gou-th/ice40-vga-controller/digital/digital_image.png

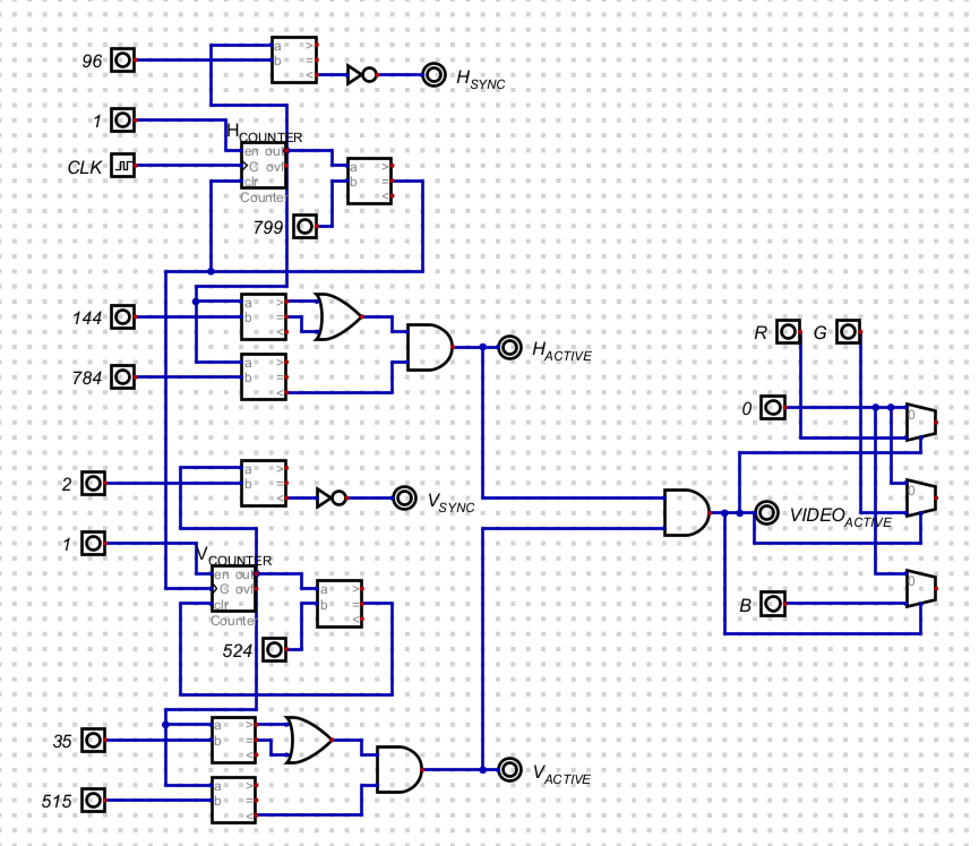
digital/digital_image.png
