gou-th/ice40-vga-controller/kicad/model/vga_3d_back.png

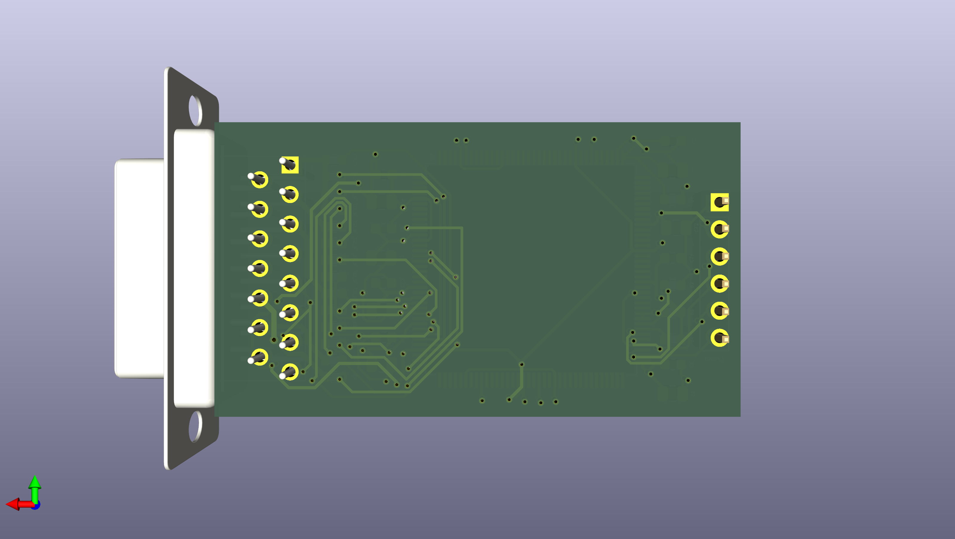
kicad/model/vga_3d_back.png
