gou-th/ice40-vga-controller/kicad/pcb/pcb_bottom_layer.png

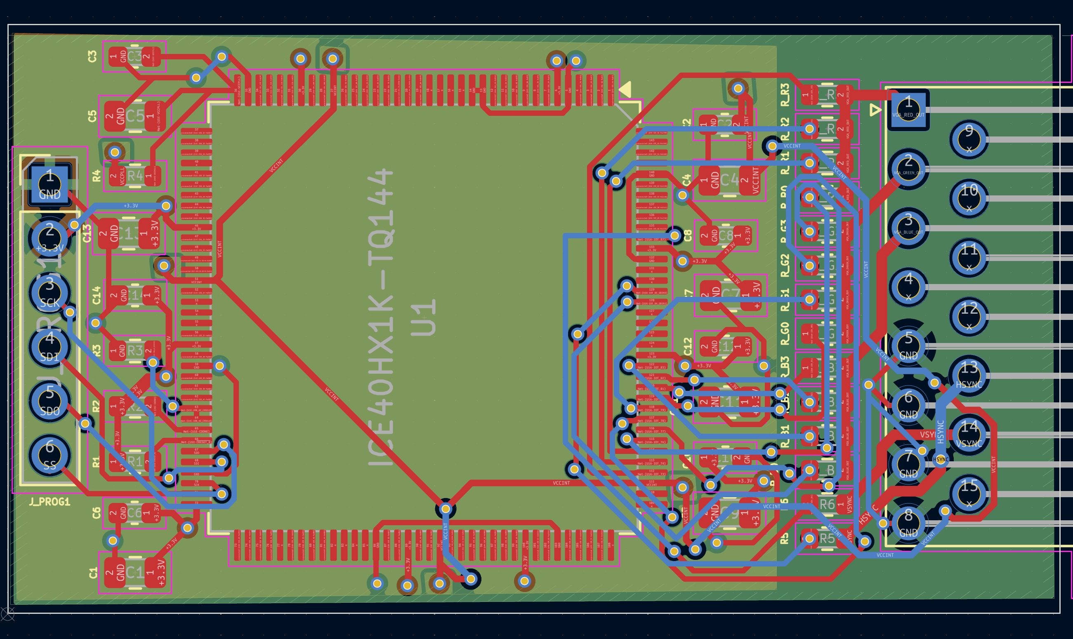
kicad/pcb/pcb_bottom_layer.png
