gou-th/ice40-vga-controller/systemverilog/sim/waveform/v_sync_end.png

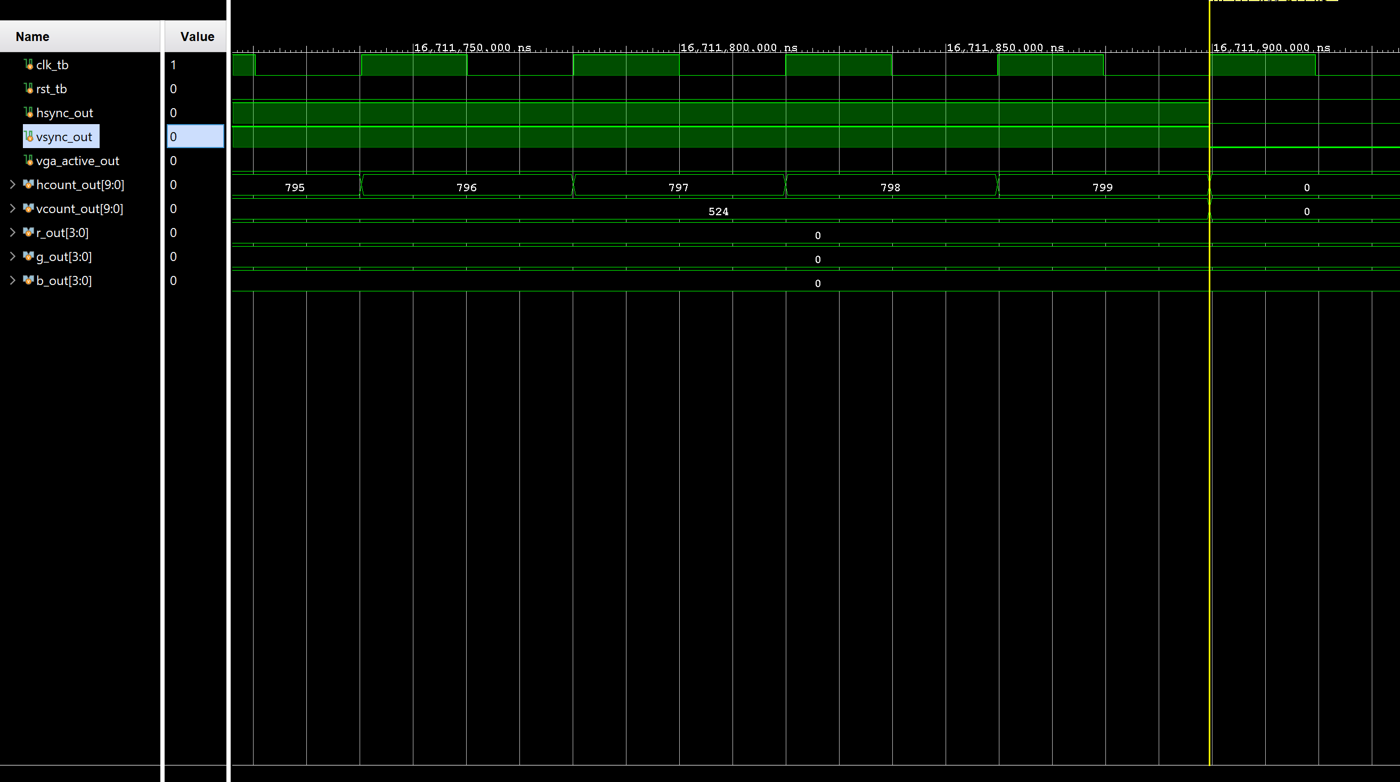
systemverilog/sim/waveform/v_sync_end.png
