gou-th/ice40-vga-controller/systemverilog/sim/waveform/v_sync_start.png

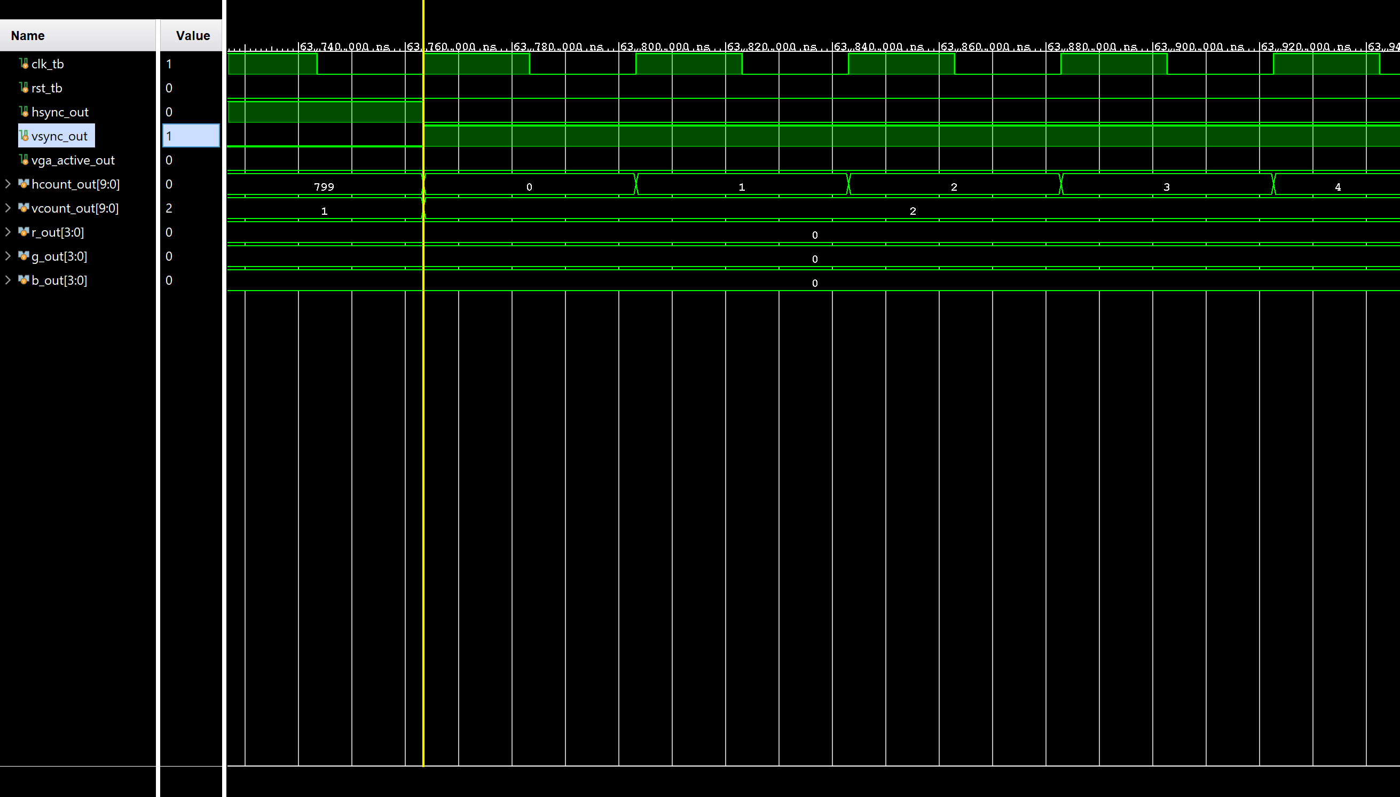
systemverilog/sim/waveform/v_sync_start.png
