gou-th/ice40-vga-controller/systemverilog/sim/waveform/vga_active_end.png

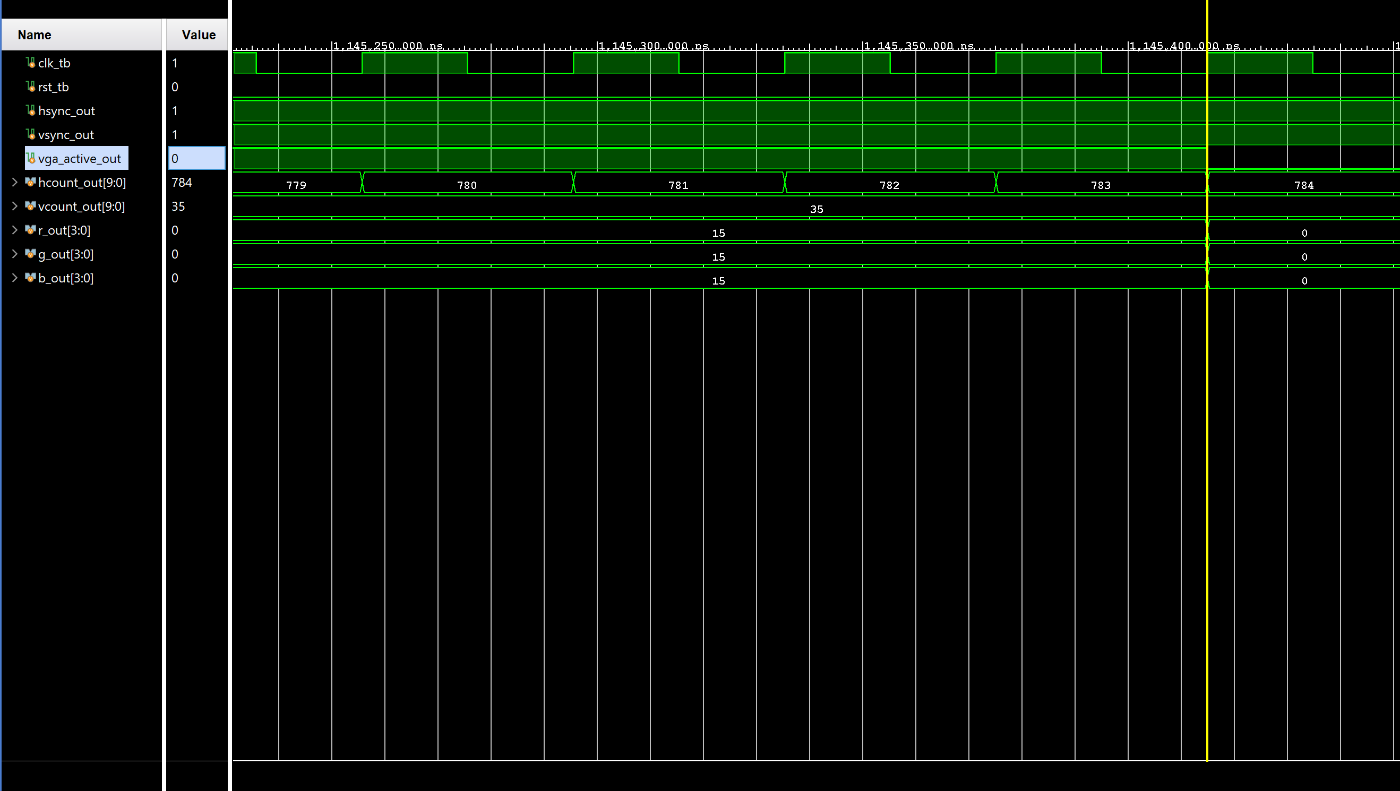
systemverilog/sim/waveform/vga_active_end.png
