gou-th/ice40-vga-controller/systemverilog/sim/waveform/vga_active_start.png

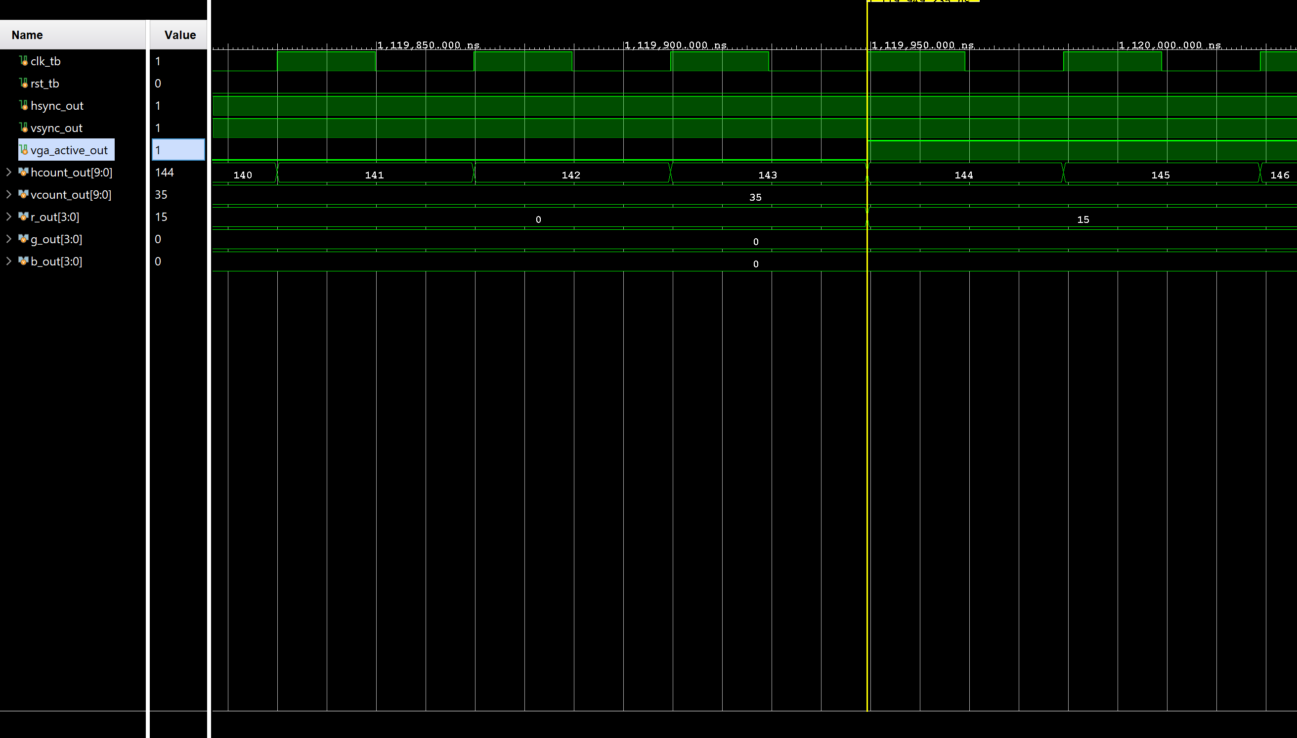
systemverilog/sim/waveform/vga_active_start.png
